viper-666/crossfire_roof_module_prototyp/Dachmodul.sch

## EAGLE design Dachmodul.sch (2017-08-15)

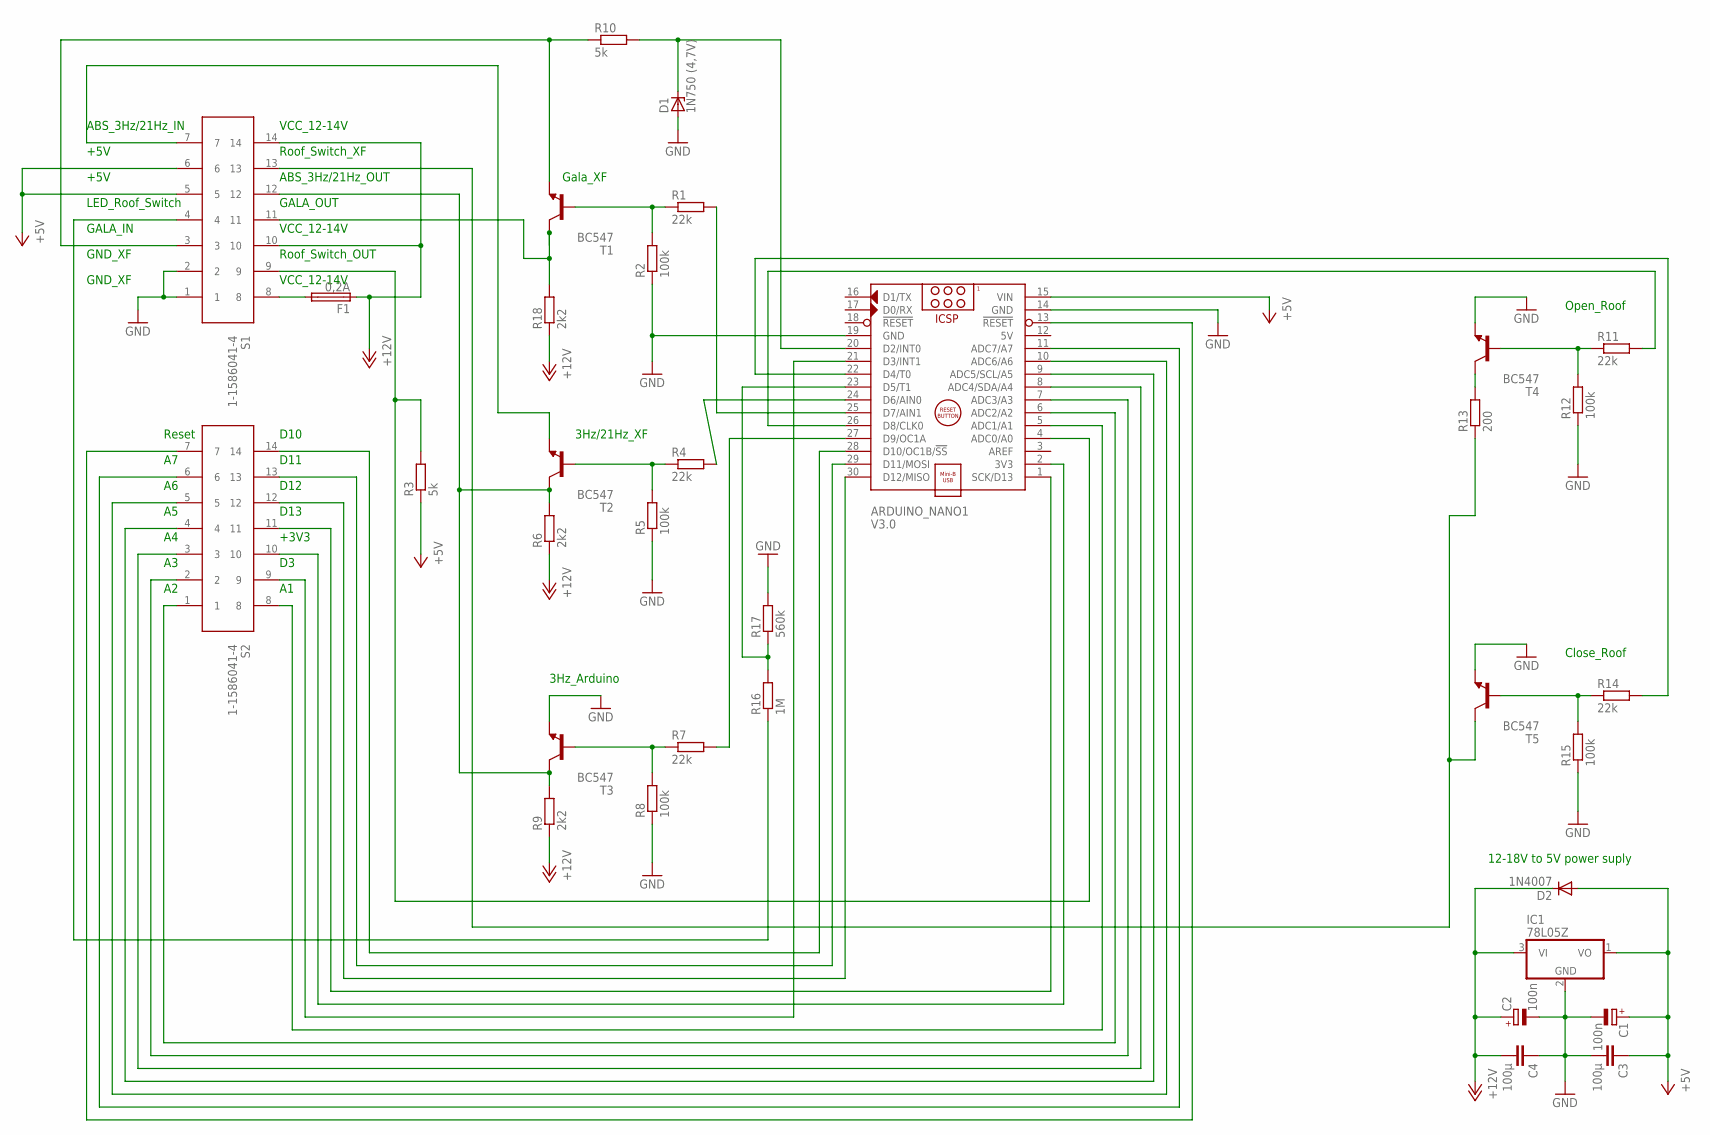
[picture p30: schematic Dachmodul.sch]

Parts:
ARDUINO_NANO1: V3.0; ARDUINO_NANO
C1, C2: 100n; E3,5-8
C3, C4: 100µ; C025-025X050
D1: 1N750 (4,7V); ZDIO-2.5
D2: 1N4007; DO41-10
F1: 0,2A; GSH15
IC1: 78L05Z; TO92
R1, R4, R7, R11, R14: 22k; 0204/5
R2, R5, R8, R12, R15: 100k; 0204/5
R3, R10: 5k; 0204/5
R6, R9: 2k2; 0204/5
R13: 200; 0204/5
R16: 1M; 0204/5
R17: 560k; 0204/5
R18: 2k2; 0204V
S1, S2: 1-1586041-4; 64901421022
T1, T2, T3, T4, T5: BC547; TO92

Connections:
+5V: ARDUINO_NANO1.15 (VIN), C1.+, C3.1, D2.A, IC1.1 (VO), R3.1, S1.5, S1.6
+12V: C2.+, C4.2, D2.C, F1.1, IC1.3 (VI), R6.1, R9.1, R18.1, S1.10, S1.14
GND: ARDUINO_NANO1.14 (GND), ARDUINO_NANO1.19 (GND), C1.-, C2.-, C3.2, C4.1, D1.A, IC1.2 (GND), R2.1, R5.1, R8.1, R12.1, R15.1, R17.2, S1.1, S1.2, T3.1 (E), T4.1 (E), T5.1 (E)
unnamed: R1.1, R2.2, T1.2 (B)
unnamed: R18.2, S1.11, T1.3 (C)
unnamed: R4.1, R5.2, T2.2 (B)
unnamed: R6.2, R9.2, S1.12, T2.3 (C), T3.3 (C)
unnamed: R7.1, R8.2, T3.2 (B)
unnamed: ARDUINO_NANO1.27 (D9/OC1A), R7.2
unnamed: S1.7, T2.1 (E)
unnamed: ARDUINO_NANO1.24 (D6/AIN0), R4.2
unnamed: R10.1, S1.3, T1.1 (E)
unnamed: ARDUINO_NANO1.25 (D7/AIN1), R1.2
unnamed: F1.2, S1.8
unnamed: R13.2, T4.3 (C)
unnamed: R11.1, R12.2, T4.2 (B)
unnamed: ARDUINO_NANO1.26 (D8/CLK0), R11.2
unnamed: R13.1, S1.13, T5.3 (C)
unnamed: R14.1, R15.2, T5.2 (B)
unnamed: ARDUINO_NANO1.22 (D4/T0), R14.2
unnamed: ARDUINO_NANO1.28 (D10/OC1B/!SS), S2.14
unnamed: R16.1, S1.4
unnamed: ARDUINO_NANO1.23 (D5/T1), R16.2, R17.1
unnamed: ARDUINO_NANO1.29 (D11/MOSI), S2.13
unnamed: ARDUINO_NANO1.30 (D12/MISO), S2.12
unnamed: ARDUINO_NANO1.1 (SCK/D13), S2.11
unnamed: ARDUINO_NANO1.2 (3V3), S2.10
unnamed: ARDUINO_NANO1.21 (D3/INT1), S2.9
unnamed: ARDUINO_NANO1.5 (ADC1/A1), S2.8
unnamed: ARDUINO_NANO1.6 (ADC2/A2), S2.1
unnamed: ARDUINO_NANO1.7 (ADC3/A3), S2.2
unnamed: ARDUINO_NANO1.8 (ADC4/SDA/A4), S2.3
unnamed: ARDUINO_NANO1.9 (ADC5/SCL/A5), S2.4
unnamed: ARDUINO_NANO1.10 (ADC6/A6), S2.5
unnamed: ARDUINO_NANO1.11 (ADC7/A7), S2.6
unnamed: ARDUINO_NANO1.13 (!RESET), S2.7
unnamed: ARDUINO_NANO1.4 (ADC0/A0), R3.2, S1.9
unnamed: ARDUINO_NANO1.20 (D2/INT0), D1.C, R10.2

Notes on the sheet:
ABS_3Hz/21Hz_OUT
ABS_3Hz/21Hz_IN
GALA_IN
GALA_OUT
VCC_12-14V
GND_XF
Roof_Switch_OUT
Roof_Switch_XF
LED_Roof_Switch
3Hz_Arduino
3Hz/21Hz_XF
Gala_XF
12-18V to 5V power suply
Open_Roof
Close_Roof
+5V
D10
D11
D12
D13
+3V3
Reset
